Jcparkyn/dpoint/python/recordings/20230905_162344/scan-original.jpg

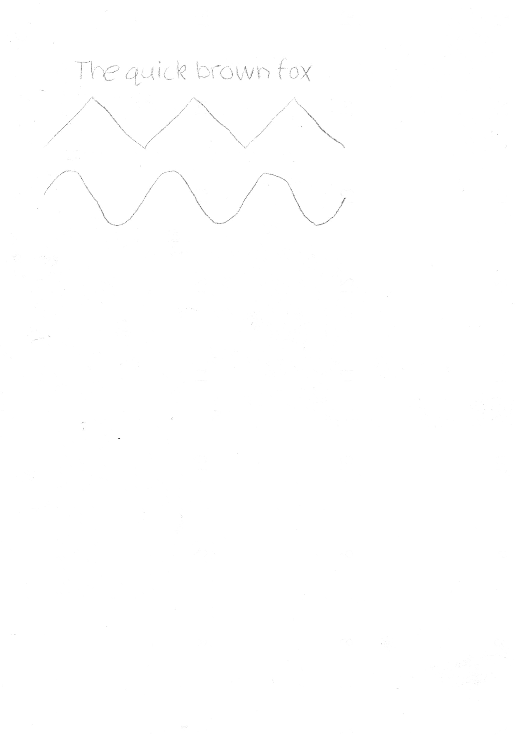
python/recordings/20230905_162344/scan-original.jpg
