Jcparkyn/dpoint/python/recordings/20230905_162344/scan.jpg

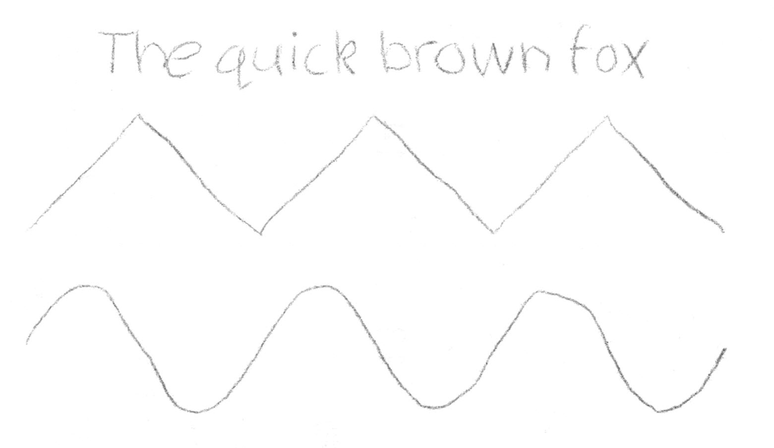
python/recordings/20230905_162344/scan.jpg
