Jcparkyn/dpoint/python/calibration_pics/f30/1687925759.jpg

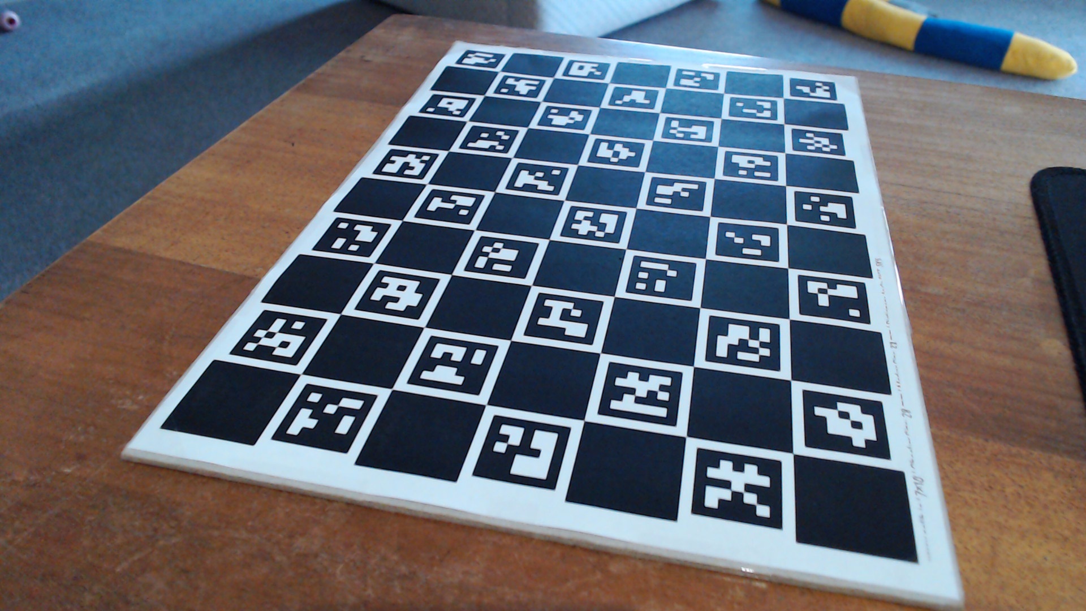
python/calibration_pics/f30/1687925759.jpg
