Jcparkyn/dpoint/python/calibration_pics/f30/1687925828.jpg

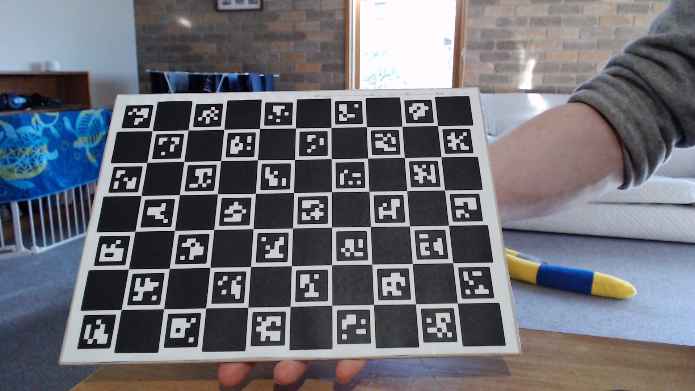
python/calibration_pics/f30/1687925828.jpg
