Jcparkyn/dpoint/python/calibration_pics/f30/1687925831.jpg

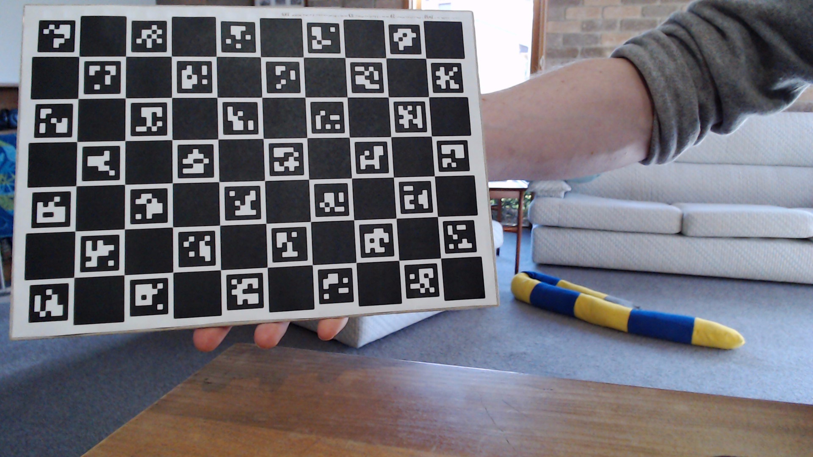
python/calibration_pics/f30/1687925831.jpg
