Jcparkyn/dpoint/python/calibration_pics/f30/1687925842.jpg

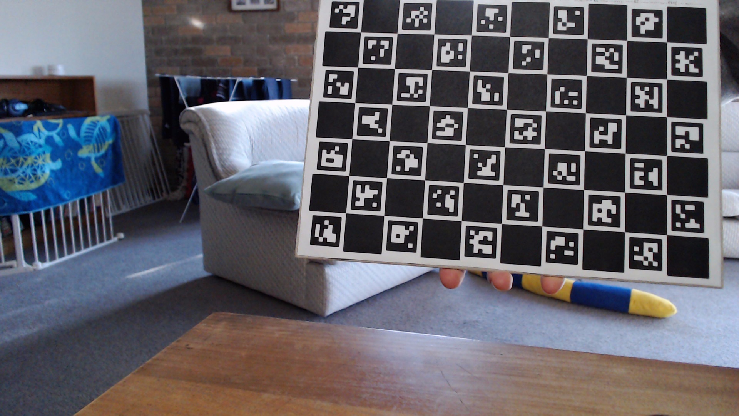
python/calibration_pics/f30/1687925842.jpg
