Jcparkyn/dpoint/python/calibration_pics/f30/1687925848.jpg

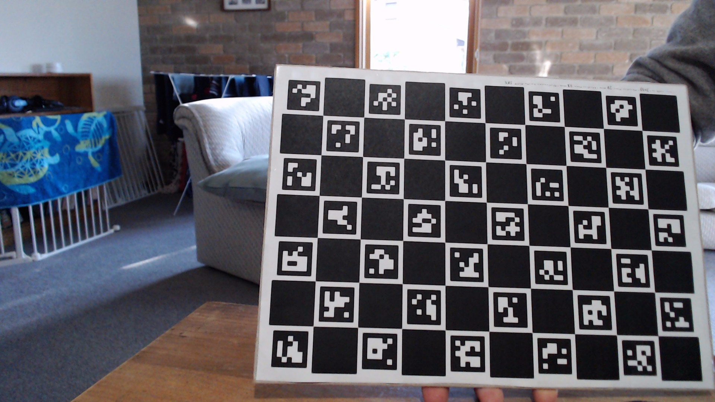
python/calibration_pics/f30/1687925848.jpg
