Jcparkyn/dpoint/python/calibration_pics/f30/1687925851.jpg

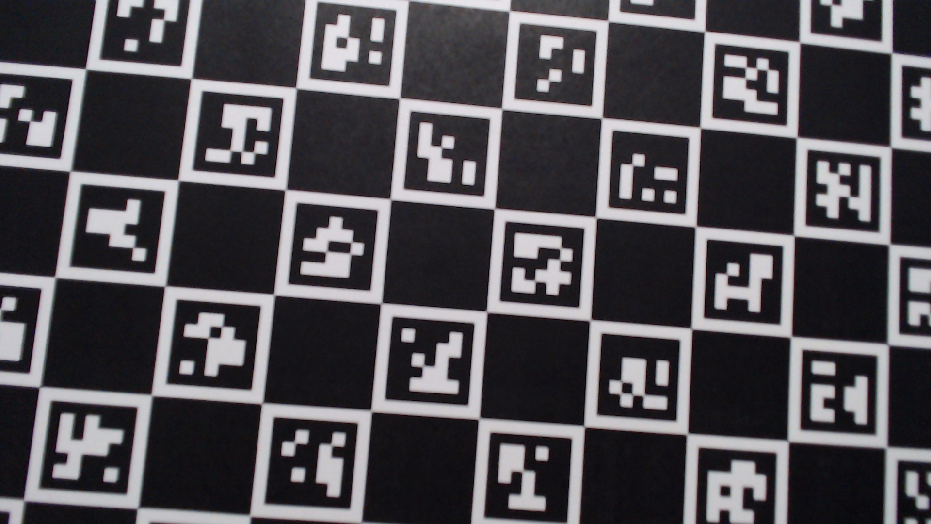
python/calibration_pics/f30/1687925851.jpg
