Jcparkyn/dpoint/python/calibration_pics/f30/1687925856.jpg

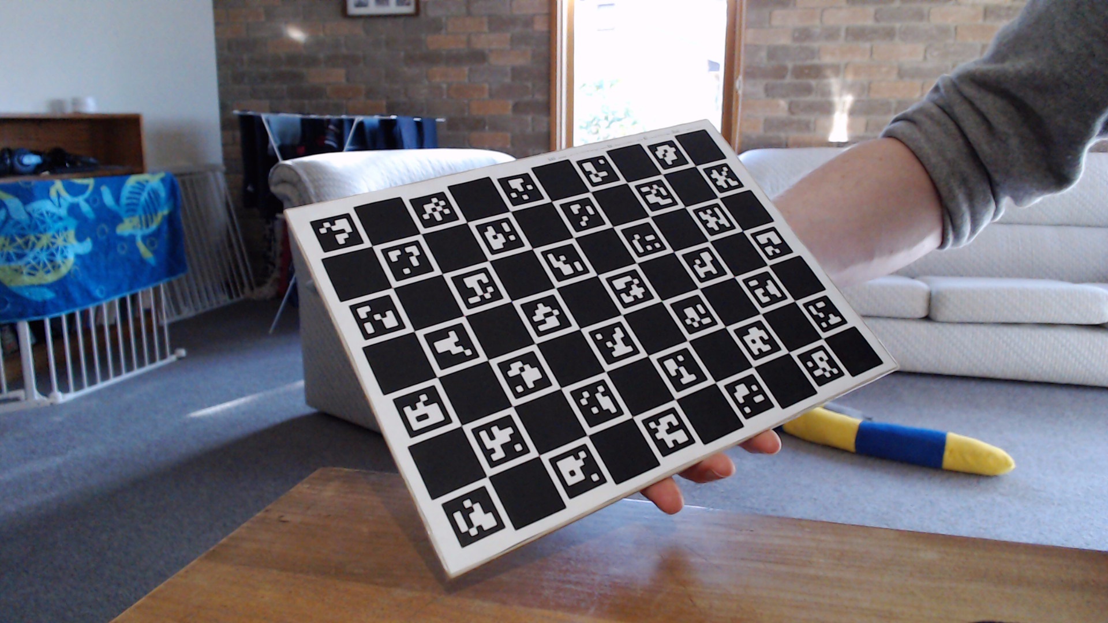
python/calibration_pics/f30/1687925856.jpg
