Jcparkyn/dpoint/python/calibration_pics/f30/1687925863.jpg

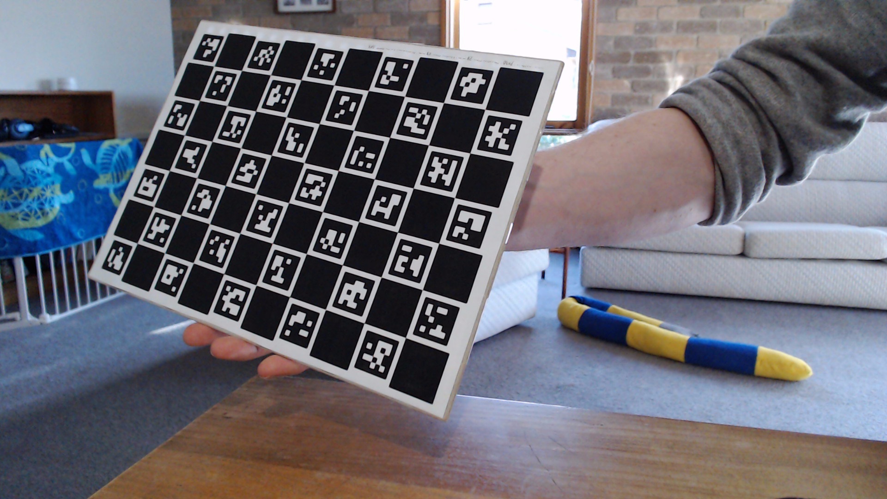
python/calibration_pics/f30/1687925863.jpg
